mike-rankin/ESP32-C3_1.54inch_E-ink/Code/One_Bit_Library/Roboto_Black_40.h

// Created by http://oleddisplay.squix.ch/ Consider a donation
// In case of problems make sure that you are using the font file with the correct version!
const uint8_t Roboto_Black_40Bitmaps[] PROGMEM = {

	// Bitmap Data:
	0x00, // ' '
	0xFE,0xFE,0xFE,0xFE,0xFE,0xFE,0xFE,0x7E,0x7E,0x7E,0x7E,0x7E,0x7E,0x7E,0x7E,0x7E,0x7E,0x7C,0x7C,0x7C,0x00,0x00,0x00,0x3C,0xFE,0xFE,0xFE,0xFE,0x3C, // '!'
	0xF1,0xEF,0x1E,0xF1,0xEF,0x1E,0xF1,0xEF,0x1E,0xF1,0xEF,0x1E,0xF1,0xCE,0x1C,0xE1,0xC0, // '"'
	0x00,0xF1,0xE0,0x01,0xE3,0xC0,0x03,0xC7,0x80,0x07,0x8F,0x00,0x1E,0x3C,0x00,0x3C,0x78,0x00,0x78,0xF0,0x00,0xF1,0xE0,0x3F,0xFF,0xFC,0x7F,0xFF,0xF8,0xFF,0xFF,0xF1,0xFF,0xFF,0xE0,0x3C,0x78,0x00,0x78,0xF0,0x00,0xF1,0xE0,0x01,0xE3,0xC0,0x07,0x87,0x01,0xFF,0xFF,0xF3,0xFF,0xFF,0xE7,0xFF,0xFF,0xCF,0xFF,0xFF,0x80,0xF1,0xE0,0x01,0xC3,0xC0,0x07,0x8F,0x00,0x0F,0x1E,0x00,0x1E,0x3C,0x00,0x3C,0x78,0x00,0x78,0xF0,0x01,0xE1,0xE0,0x00, // '#'
	0x00,0x70,0x00,0x07,0x00,0x00,0x70,0x00,0x07,0x00,0x03,0xFC,0x00,0xFF,0xF0,0x1F,0xFF,0x83,0xFF,0xFC,0x7F,0xFF,0xC7,0xF0,0xFE,0x7E,0x0F,0xE7,0xE0,0x7E,0x7E,0x07,0xE7,0xE0,0x00,0x7F,0x00,0x07,0xF8,0x00,0x3F,0xF0,0x01,0xFF,0xC0,0x0F,0xFE,0x00,0x3F,0xF8,0x00,0xFF,0xC0,0x03,0xFC,0x00,0x0F,0xE0,0x00,0xFE,0xFC,0x07,0xEF,0xC0,0x7E,0xFE,0x0F,0xEF,0xF0,0xFE,0x7F,0xFF,0xE7,0xFF,0xFC,0x3F,0xFF,0x80,0xFF,0xF0,0x03,0xFC,0x00,0x0E,0x00,0x00,0xE0,0x00,0x0E,0x00,0x00,0xE0,0x00, // '$'
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
	  {  2248,  21,  29,  23,    2,  -29 }, // 'E'
	  {  2325,  20,  29,  23,    2,  -29 }, // 'F'
	  {  2398,  25,  29,  28,    1,  -29 }, // 'G'
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
};
const GFXfont Roboto_Black_40 PROGMEM = {
(uint8_t  *)Roboto_Black_40Bitmaps,(GFXglyph *)Roboto_Black_40Glyphs,0x20, 0x7E, 48};
