mike-rankin/ESP32-C3_1.54inch_E-ink/Code/Sensor_Test/Sensor_Test.ino

/*************************************************** 
  This is an example for the SHTC3 Humidity & Temp Sensor

  Designed specifically to work with the SHTC3 sensor from Adafruit
  ----> https://www.adafruit.com/products/4636

  These sensors use I2C to communicate, 2 pins are required to  
  interface
 ****************************************************/

#include "Adafruit_SHTC3.h"

Adafruit_SHTC3 shtc3 = Adafruit_SHTC3();

void setup() 
{
  Serial.begin(115200);
  Wire.begin(8,2);

  while (!Serial)
    delay(10);     // will pause Zero, Leonardo, etc until serial console opens

  Serial.println("SHTC3 test");
  if (! shtc3.begin()) {
    Serial.println("Couldn't find SHTC3");
    while (1) delay(1);
  }
  Serial.println("Found SHTC3 sensor");
}


void loop() {
  sensors_event_t humidity, temp;
  
  shtc3.getEvent(&humidity, &temp);// populate temp and humidity objects with fresh data
  
  Serial.print("Temperature: "); Serial.print(temp.temperature); Serial.println(" degrees C");
  Serial.print("Humidity: "); Serial.print(humidity.relative_humidity); Serial.println("% rH");

  delay(1000);
}
